Acramonics/ButterworthScopeFilter/LTSpice/AntiAlias_40kHz.asc

C1: cap; 1nF
C2: cap; 1nF
C3: cap; 1nF
R1: res; 3.92k
R2: res; 1.33k
R3: res; 3.92k
R4: res; 3.92k
R5: res; 3.48k
U1: OP727
U2: OP727
U3: OP727
V1: voltage; SINE(0 0.1 1000); AC 0.1
V2: voltage; 5
V3: voltage; 5
Named nets: in, out, 0
.ac oct 5000 10 100k
