Acramonics/ButterworthScopeFilter/LTSpice/Butterworth_Active_50kHz.asc

C1: cap; 1.2nF
C2: cap; 3.3nF
C3: cap; 3.3nF
C4: cap; 8.2nF
R1: res; 1k
R2: res; 1k
R3: res; 1k
R4: res; 1k
U1: OP727
U2: OP727
V1: voltage; SINE(0 0.1 1000); AC 0.1
V2: voltage; 5
V3: voltage; 5
Named nets: in, out, 0
.ac oct 5000 10 100k
